elkayem/usbMIDI2CV_MC/images/IMG_1628.JPG

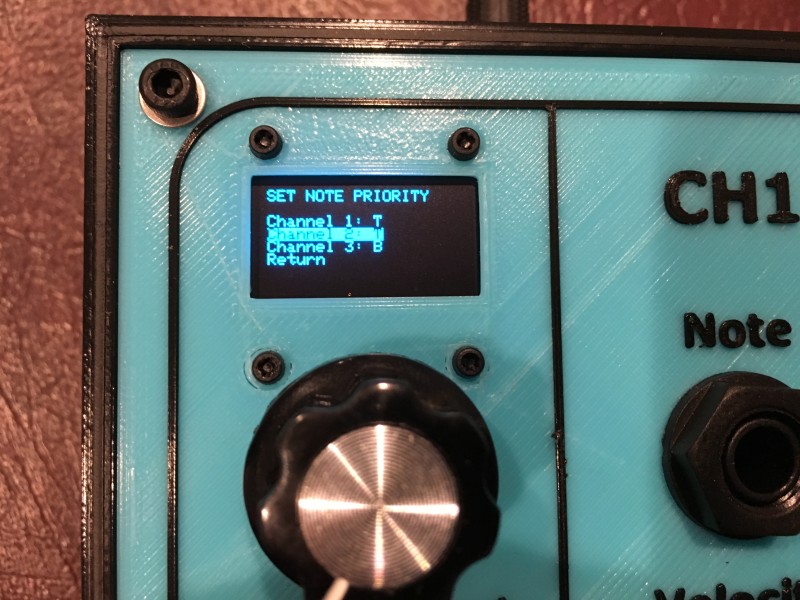
images/IMG_1628.JPG
